telzo2000/cool640zmk/img/img00003.jpg

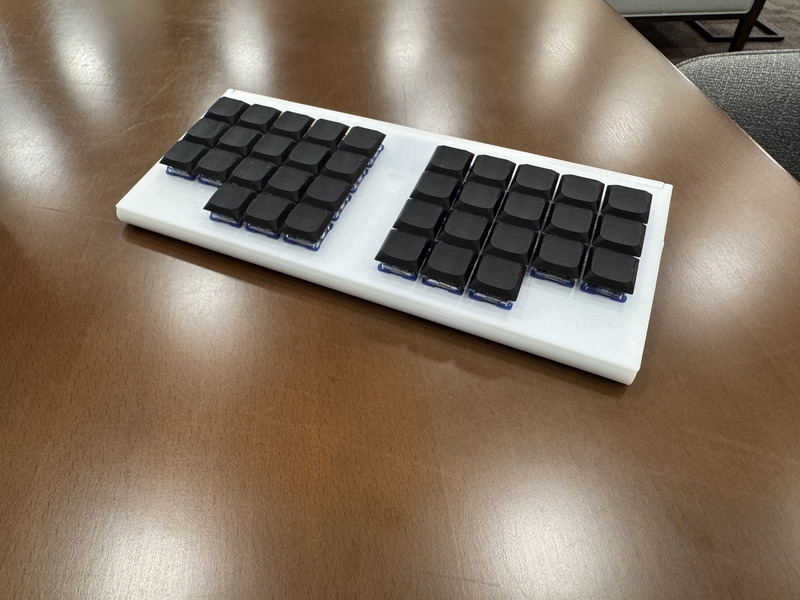
img/img00003.jpg
