telzo2000/cool640zmk/img/img00004.jpg

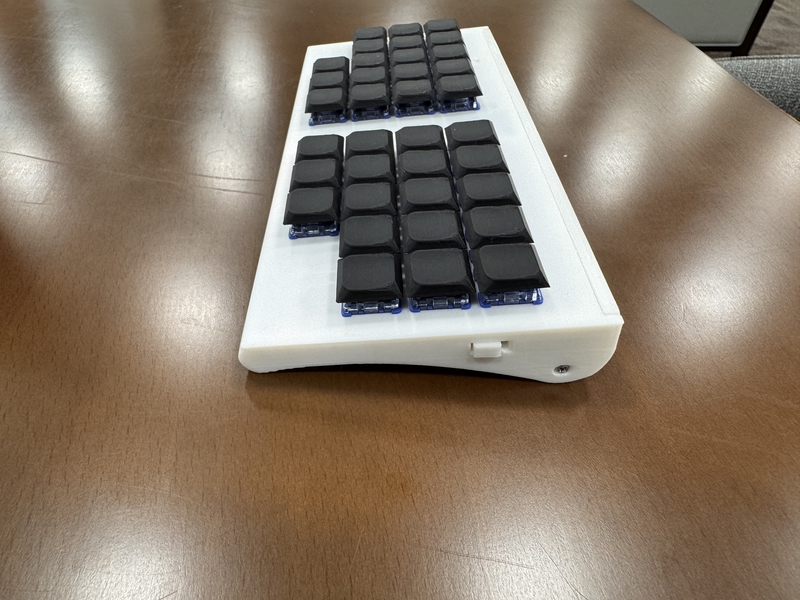
img/img00004.jpg
