telzo2000/cool640zmk/img/img00005.jpg

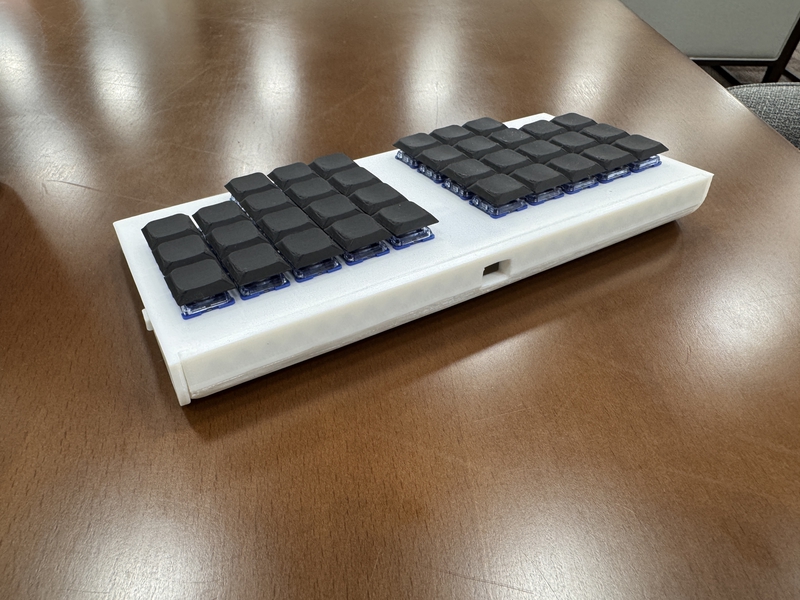
img/img00005.jpg
