telzo2000/cool640zmk/img/img00006.jpg

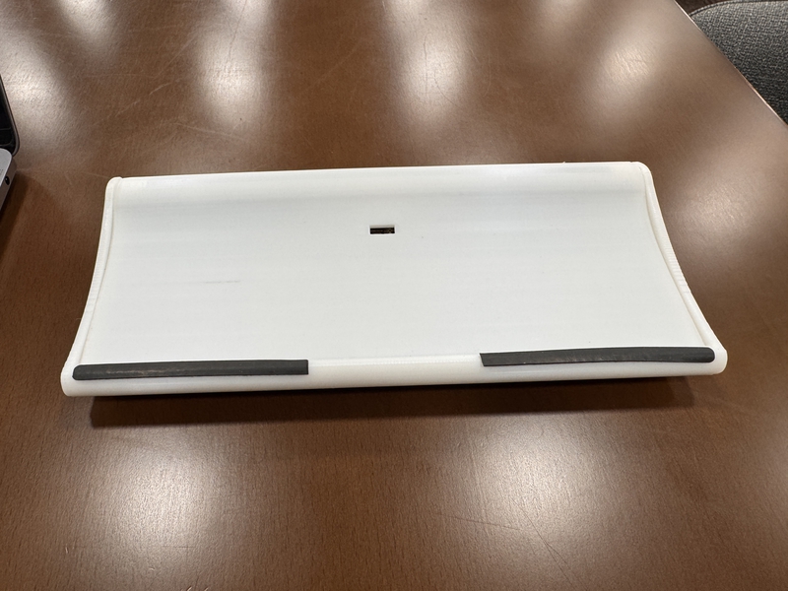
img/img00006.jpg
