telzo2000/cool640zmk/img/img00007.jpg

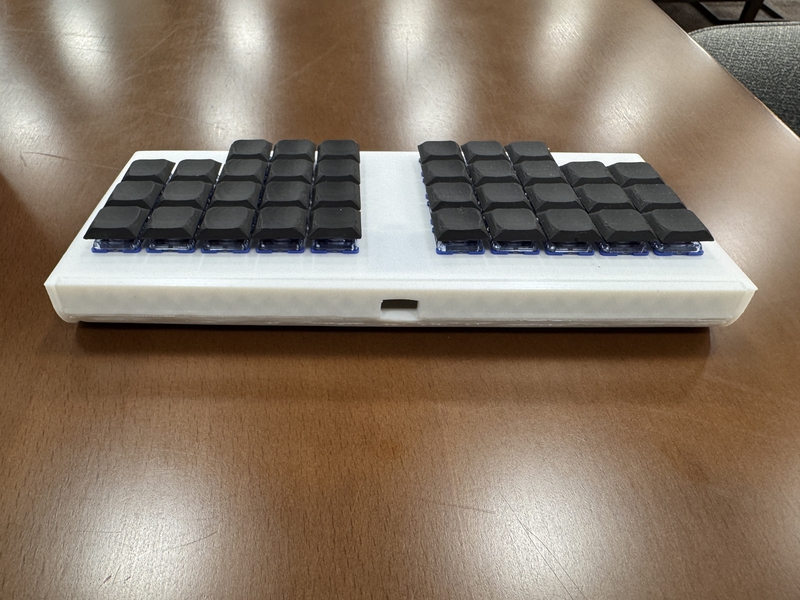
img/img00007.jpg
