telzo2000/cool640zmk/img/img00008.jpg

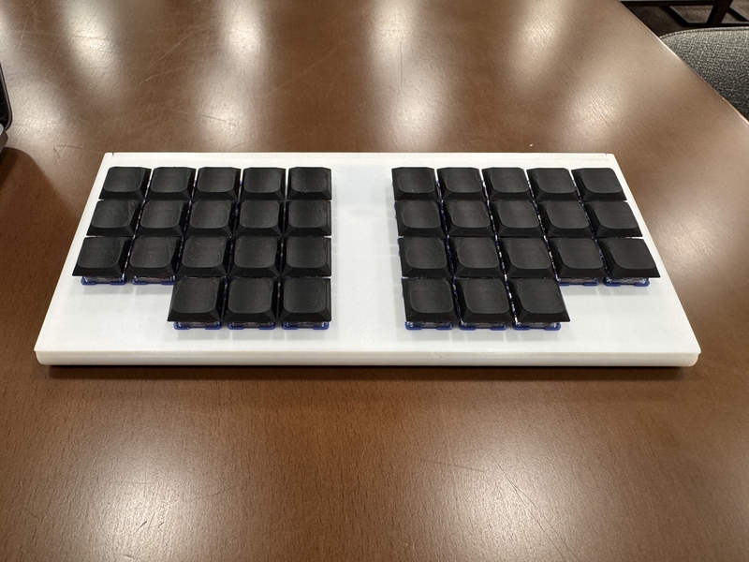
img/img00008.jpg
